borti4938/SNES_MultiRegion_with_DeJitter_QID/installation/SNS-CPU-GPM-02/backside_labeled.jpg

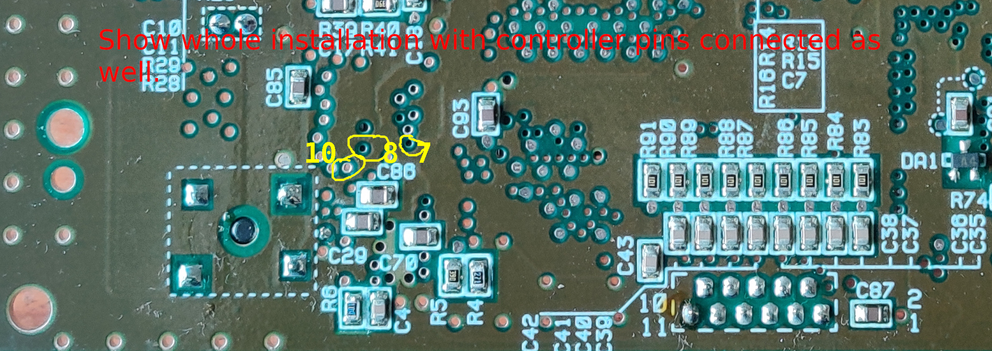
installation/SNS-CPU-GPM-02/backside_labeled.jpg
