borti4938/SNES_MultiRegion_with_DeJitter_QID/installation/SNSP-CPU-01/CIC_Clk.jpg

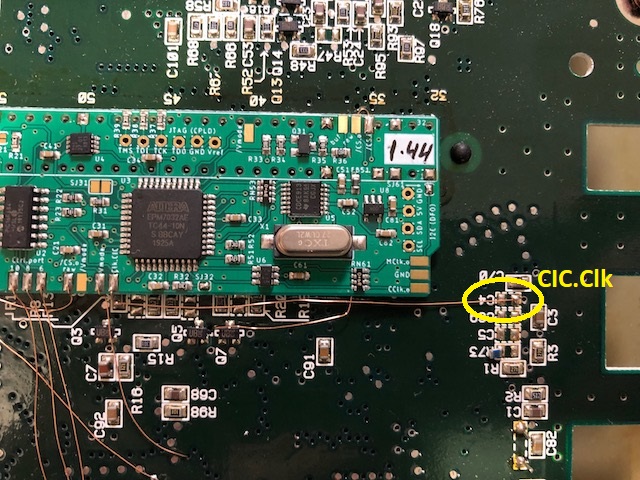
installation/SNSP-CPU-01/CIC_Clk.jpg
