borti4938/SNES_MultiRegion_with_DeJitter_QID/fw/uIGR/snes_uigr_684.asm

    #include <p16f684.inc>

; -----------------------------------------------------------------------
;   SNES "In-game reset" (IGR) controller for use with the SuperCIC only
;
;   Copyright (C) 2010 by Maximilian Rehkopf <otakon@gmx.net>
;
;   Last Modified: Dec. 2015 by Peter Bartmann <borti4938@gmx.de>
;
;   This program is free software; you can redistribute it and/or modify
;   it under the terms of the GNU General Public License as published by
;   the Free Software Foundation; version 2 of the License only.
;
;   This program is distributed in the hope that it will be useful,
;   but WITHOUT ANY WARRANTY; without even the implied warranty of
;   MERCHANTABILITY or FITNESS FOR A PARTICULAR PURPOSE.  See the
;   GNU General Public License for more details.
;
;   You should have received a copy of the GNU General Public License
;   along with this program; if not, write to the Free Software
;   Foundation, Inc., 59 Temple Place, Suite 330, Boston, MA  02111-1307  USA
;
; -----------------------------------------------------------------------
;
;   This program is designed to run on a PIC 16F684 microcontroller connected
;   to the controller port and SNES main board. It allows an SNES to be reset
;   and region switched via a standard controller. This version of the code
;   shall be used only in combination with the SCIC!
;
;   pin configuration: (controller port pin) [other connection]
;
;                                                 ,-----_-----.
;        +5V (1) [mb front 1 and many others :-)] |1        14| GND (7) [mb front 11 and many others :-)]
;   Reset in/out [to CIC pin 8 / SuperCIC pin 13] |2  A5 A0 13| serial data in(4) [mb front 6(*)]
;                           50/60Hz out [to PPUs] |3  A4 A1 12| latch in(3)       [mb front 10]
;               Cart-Region [from SuperCIC pin 3] |4  A3 A2 11| clk in(2)         [mb front 8(**)]
;                        LED out - grn, 50Hz Mode |5  C5 C0 10| LED in - grn [from SuperCIC pin 5]
;                        LED out - red, 60Hz Mode |6  C4 C1  9| LED in - red [from SuperCIC pin 6]
;                 $213f-D4-Patch enable out (***) |7  C3 C2  8| LED_TYPE in  [from SuperCIC pin 7] (****)
;                                                 `-----------'
;
;   (*)
;     use pin 4 at mb front ctrl.panel connector instead of pin 6 if you want to
;     use the IGR-functions with player 2
;   (**)
;     use pin 9 at mb front ctrl.panel connector instead of pin 8 if you want to
;     use the IGR-functions with player 2
;   (***)
;     Pin 7 can be left open if no $213f-D4-Patch is build in the console.
;     Otherwise this pin has to be connected to one input of the 74*133 IC of the
;     patch. Logic is positive.
;   (***)
;     Pin 8 (LED_TYPE) sets the output mode for the LED pins
;     (must be tied to either level):
;       low  = common cathode
;       high = common anode   (output inverted)
;
;
;   As the internal oscillator is used, you should connect a capacitor of about 100nF between
;   Pin 1 (Vdd/+5V) and Pin 14 (Vss/GND) as close as possible to the PIC. This esures best
;   operation
;
;   controller pin numbering
;   ========================
;        _______________________________
;       |                 |             \
;       | (1) (2) (3) (4) | (5) (6) (7)  ) (player 1 or player 2 can be used)
;       |_________________|_____________/
;
;
;   key mapping: L + R + Select +                                (stream data)
;   =============================
;   Start        Reset (normal)                                  0xcf 0xcf
;   X            Reset (double)                                  0xdf 0x8f
;
;   Y            Region 50Hz/PAL                                 0x9f 0xcf
;   A            Region 60Hz/NTSC                                0xdf 0x4f
;   B            Region from Cartridge                           0x5f 0xcf
;   D-Pad left   Region from SCIC                                0xdd 0xcf
;   D-Pad right  Region from SCIC                                0xde 0xcf
;
;   D-Pad up     Toggle the region timeout                       0xd7 0xcf
;   D-Pad down   Toggle $213f-D4-Patch enable/disable            0xdb 0xcf
;
;   Toggle region timeout:
;   LED confirms with
;     - region timeout switched on : red   -> yellow -> green
;     - region timeout switched off: green -> yellow -> red
;
;   Toggle region patch:
;   LED confirms with
;     - region patch switched on : green -> off -> green
;     - region patch switched off: red   -> off -> red
;
;   Lock Type 1:
;   To lock all other combinations one may press (D-Pad left + D-Pad up + L +
;   R + A + X -> strean data 0xf5 0x0f) together. The same combination unlocks
;   the IGR functionalities again.
;   Lock   -> LED confirms with fast flashing red
;   Unlock -> LED confirms with fast flashing green
;
;   Lock Type 2:
;   To lock all combinations one may press (D-Pad down + D-Pad left + L +
;   R + A + B -> strean data 0x79 0x4f) together. This can only be undone by
;   a reset (only reset button, not by sd2snes-IGRs) or power off and on again
;   Lock   -> LED confirms with fast flashing red
;
;
;   functional description:
;   =======================
;   Reset (normal):        simply resets the console.
;   Reset (double):        resets the console twice to enter main menu on
;                          PowerPak (due to initilize a long reset at SCIC)
;                          and sd2snes (double reset detection in firmware).
;
;   Region 50Hz/PAL        overrides the region to 50Hz/PAL.
;   Region 60Hz/NTSC       overrides the region to 60Hz/NTSC.
;   Region from cartridge  sets the region according to the input level of
;                          pin 4 (+5V = 50Hz, 0V = 60Hz).
;   Region from SuperCIC   sets the region according to the input level of
;                          the led (pin 8, 9 and 10) the current mode (50Hz,
;                          60Hz or Auto) is calculated by the uIGR. In this mode
;                          the region is updated periodically.
;
;   Toggle region timeout  for ~9s the console stays in the region mode of the
;                          cartridge and switches then into the last user mode
;   Toggle region patch    enables or disables the d4-patch over pin 7
;                          (0V = disable, +5V = enable)
;
;
;   Support of retro-bit wireless controllers:
;   ==========================================
;   These controllers have a long delay from signalling a button bit change by
;   the SNES until the bit is set on the dataline. This is not a problem if the
;   auto joypad read (AJR) is enabled. However, if AJR is not, this may harm the
;   respondence of the uIGR (as the uIGR might not have enough time to store the
;   button bit). Hence I decided to introduce a new finger breaking button combo
;   to switch on and off the long delays (and hence the support of retro-bit
;   wireless controllers).
;   This combo is:
;     - L+R+St+B+Y+A+X (stream data: 0x2f 0x0f)
;   The uIGR confirms with LED color codes:
;     - support switched on : green -> yellow -> green
;     - support switched off: red   -> yellow -> red
;
;
; -----------------------------------------------------------------------
; Configuration bits: adapt to your setup and needs
    __CONFIG _INTOSCIO & _IESO_OFF & _WDT_OFF & _PWRTE_OFF & _MCLRE_OFF & _CP_OFF & _CPD_OFF & _BOD_OFF

with_lock             set 1 ; 0 = without locking combination
                            ; 1 = with locking combinations
default_with_regpatch set 1 ; 0 = default set to 60Hz and region timeout enabled
                            ; 1 = default set to 60Hz and region patch enabled
                            ;     (for installations without or with region patch)

; -----------------------------------------------------------------------
; macros and definitions

M_movff macro   fromReg, toReg  ; move filereg to filereg
        movfw   fromReg
        movwf   toReg
        endm

M_movpf macro   fromPORT, toReg ; move PORTx to filereg
        movfw   fromPORT
        andlw   0x3f
        movwf   toReg
        endm

M_movlf macro   literal, toReg  ; move literal to filereg
        movlw   literal
        movwf   toReg
        endm

M_beff  macro   compReg1, compReg2, branch  ; branch if two fileregs are equal
        movfw   compReg1
        xorwf   compReg2, w
        btfsc   STATUS, Z
        goto    branch
        endm

M_bepf  macro   compPORT, compReg, branch   ; branch if PORTx equals compReg (ignoring bit 6 and 7)
        movfw   compPORT
        xorwf   compReg, w
        andlw   0x3f
        btfsc   STATUS, Z
        goto    branch
        endm

M_belf  macro   literal, compReg, branch  ; branch if a literal is stored in filereg
        movlw   literal
        xorwf   compReg, w
        btfsc   STATUS, Z
        goto    branch
        endm

M_delay_x05ms   macro   literal ; delay about literal x 05ms
                movlw   literal
                movwf   reg_repetition_cnt
                call    delay_x05ms
                endm

M_T1reset   macro   ; reset and start timer1
            clrf    TMR1L
            clrf    TMR1H
            clrf    PIR1
            bsf     T1CON, TMR1ON
            endm

M_StBuToRegF    macro   button, toReg  ; store button to register (fast)
                btfsc   PORTA, CTRL_DATA
                bsf     toReg, button
                btfss   INTCON, INTF
                goto    $-1
                endm

M_StBuToReg macro   button, toReg  ; store button to register
            btfss   PORTA, CTRL_CLK
            goto    $-1
            nop
            bcf     INTCON, INTF
            btfsc   PORTA, CTRL_DATA
            bsf     toReg, button
            btfss   INTCON, INTF
            goto    $-1
            endm

M_StBuToRegRBWC macro   button, toReg  ; store button to register (Retro-Bit Wireless Controller)
                btfss   PORTA, CTRL_CLK
                goto    $-1
                goto    $+1 ; 2-cycle-delay
                nop
                bcf     INTCON, INTF
                nop
                btfsc   PORTA, CTRL_DATA
                bsf     toReg, button
                btfss   INTCON, INTF
                goto    $-1
                endm

M_push_reset    macro   ; push reset button
                banksel TRISA
                bcf     TRISA, RESET_OUT
                banksel PORTA
                bsf     PORTA, RESET_OUT
                endm

M_release_reset macro   ; push release button
                bcf     PORTA, RESET_OUT
                banksel TRISA
                bsf     TRISA, RESET_OUT
                banksel PORTA
                endm

M_setAuto   macro   ; set modeout to auto
            btfsc   PORTA, CART_MODE_IN
            set50Hz
            btfss   PORTA, CART_MODE_IN
            set60Hz
            endm

#define set60Hz     bcf PORTA, MODE_OUT
#define set50Hz     bsf PORTA, MODE_OUT
#define setD4on     bsf PORTC, REGPATCH_OUT
#define setD4off    bcf PORTC, REGPATCH_OUT

; -----------------------------------------------------------------------
; bits and registers and more

CTRL_DATA       EQU 0
CTRL_LATCH      EQU 1
CTRL_CLK        EQU 2
CART_MODE_IN    EQU 3
MODE_OUT        EQU 4
RESET_IN        EQU 5
RESET_OUT       EQU 5

LED_MODE_50_IN  EQU 0
LED_MODE_60_IN  EQU 1
LED_TYPE_IN     EQU 2
REGPATCH_OUT    EQU 3

reg_ctrl_data_lsb       EQU 0x20
reg_ctrl_data_msb       EQU 0x21
reg_ctrl_read_ready     EQU 0x22
reg_t0_overflows        EQU 0x31
reg_repetition_cnt      EQU 0x32
reg_t1_overflows        EQU 0x33
reg_current_mode        EQU 0x40
reg_passthru_calc       EQU 0x41
reg_led_save            EQU 0x42

bit_mode_scic       EQU 0
bit_mode_auto       EQU 1
bit_mode_50_60      EQU 2
bit_rbwc_support    EQU 3
bit_regtimeout      EQU 4
bit_regpatch        EQU 5

    
code_mode_scic    EQU (1<<bit_mode_scic)      ; 0x01
code_mode_auto    EQU (1<<bit_mode_auto)      ; 0x02
code_mode_60      EQU (0<<bit_mode_50_60)     ; 0x00
code_mode_50      EQU (1<<bit_mode_50_60)     ; 0x04
code_rbwc_support EQU (1<<bit_rbwc_support)   ; 0x08
code_regtimeout   EQU (1<<bit_regtimeout)     ; 0x10
code_regpatch     EQU (1<<bit_regpatch)       ; 0x20

  if with_lock
    bit_igrlock_tmp     EQU 6
    bit_igrlock_ever    EQU 7

    code_igrlock_tmp    EQU (1<<bit_igrlock_tmp)    ; 0x40
  endif

code_led_off    EQU 0x00    ; off
code_led_60     EQU 0x10    ; red
code_led_50     EQU 0x20    ; green
code_led_auto   EQU 0x30    ; yellow
code_invert_led EQU 0x30    ; to invert the LED (needed if a com. anode LED is used)

  if default_with_regpatch
    code_mode_default   EQU (code_mode_60 ^ code_regpatch)
  else
    code_mode_default   EQU (code_mode_60 ^ code_regtimeout)
  endif

delay_05ms_t0_overflows     EQU 0x14    ; prescaler T0 set to 1:2
repetitions_60ms            EQU 0x0c
repetitions_200ms           EQU 0x28
repetitions_260ms           EQU 0x34
repetitions_580ms           EQU 0x74
repetitions_LED_delay       EQU 0x78    ; around 600ms
repetitions_LED_delay_fast  EQU 0x3c    ; around 300ms

overflows_t1_regtimeout_start       EQU 0xa3
overflows_t1_regtimeout_reset       EQU 0xa3
overflows_t1_regtimeout_reset_2     EQU 0x9b
overflows_t1_regtimeout_dblrst      EQU 0xff
overflows_t1_regtimeout_dblrst_2    EQU 0xfb

; -----------------------------------------------------------------------
; buttons

BUTTON_B    EQU 7
BUTTON_Y    EQU 6
BUTTON_SL   EQU 5
BUTTON_ST   EQU 4
DPAD_UP     EQU 3
DPAD_DW     EQU 2
DPAD_LE     EQU 1
DPAD_RI     EQU 0

BUTTON_A    EQU 7
BUTTON_X    EQU 6
BUTTON_L    EQU 5
BUTTON_R    EQU 4

BUTTON_NONE3    EQU 3
BUTTON_NONE2    EQU 2
BUTTON_NONE1    EQU 1
BUTTON_NONE0    EQU 0

; -----------------------------------------------------------------------

; code memory
 org    0x0000
    clrf    STATUS      ; 00h Page 0, Bank 0
    nop                 ; 01h
    nop                 ; 02h
    goto    start       ; 03h Initialisierung / ProgrammBeginn


; --------ISR--------
 org    0x0004  ; jump here on interrupt with GIE set
CtrlRead_ISR
    M_movlf ((1<<INTE)^(1<<RAIE)), INTCON
    btfsc   reg_current_mode, bit_rbwc_support
    goto    CtrlRead_ISR_RBWC
    
; button B can be read immediately (nearly, 4 instruction cycles until this  macro is reached)
    M_StBuToRegF  BUTTON_B, reg_ctrl_data_msb
    
; before button Y is stored, unset RAIF (from now on, no IOC at the data latch shall appear)
    btfss   PORTA, CTRL_CLK
    goto    $-1
    bcf     INTCON, INTF
    bcf     INTCON, RAIF
    M_StBuToRegF  BUTTON_Y, reg_ctrl_data_msb

; read all other buttons afterwards
    M_StBuToReg BUTTON_SL, reg_ctrl_data_msb
    M_StBuToReg BUTTON_ST, reg_ctrl_data_msb
    M_StBuToReg DPAD_UP,   reg_ctrl_data_msb
    M_StBuToReg DPAD_DW,   reg_ctrl_data_msb
    M_StBuToReg DPAD_LE,   reg_ctrl_data_msb
    M_StBuToReg DPAD_RI,   reg_ctrl_data_msb
    
    M_StBuToReg BUTTON_A,     reg_ctrl_data_lsb
    M_StBuToReg BUTTON_X,     reg_ctrl_data_lsb
    M_StBuToReg BUTTON_L,     reg_ctrl_data_lsb
    M_StBuToReg BUTTON_R,     reg_ctrl_data_lsb
    M_StBuToReg BUTTON_NONE3, reg_ctrl_data_lsb
    M_StBuToReg BUTTON_NONE2, reg_ctrl_data_lsb
    M_StBuToReg BUTTON_NONE1, reg_ctrl_data_lsb
    M_StBuToReg BUTTON_NONE0, reg_ctrl_data_lsb

    goto  check_controller_read
    
CtrlRead_ISR_RBWC
; button B can be read immediately (nearly, 5 instruction cycles until this  macro is reached)
    M_StBuToRegF  BUTTON_B, reg_ctrl_data_msb
    
; before button Y is stored, unset RAIF (from now on, no IOC at the data latch shall appear)
    btfss   PORTA, CTRL_CLK
    goto    $-1
    goto    $+1  ; 2-cycle-delay
    nop
    bcf     INTCON, INTF
    bcf     INTCON, RAIF
    M_StBuToRegF  BUTTON_Y, reg_ctrl_data_msb

; read all other buttons afterwards
    M_StBuToRegRBWC BUTTON_SL, reg_ctrl_data_msb
    M_StBuToRegRBWC BUTTON_ST, reg_ctrl_data_msb
    M_StBuToRegRBWC DPAD_UP,   reg_ctrl_data_msb
    M_StBuToRegRBWC DPAD_DW,   reg_ctrl_data_msb
    M_StBuToRegRBWC DPAD_LE,   reg_ctrl_data_msb
    M_StBuToRegRBWC DPAD_RI,   reg_ctrl_data_msb
    
    M_StBuToRegRBWC BUTTON_A,     reg_ctrl_data_lsb
    M_StBuToRegRBWC BUTTON_X,     reg_ctrl_data_lsb
    M_StBuToRegRBWC BUTTON_L,     reg_ctrl_data_lsb
    M_StBuToRegRBWC BUTTON_R,     reg_ctrl_data_lsb
    M_StBuToRegRBWC BUTTON_NONE3, reg_ctrl_data_lsb
    M_StBuToRegRBWC BUTTON_NONE2, reg_ctrl_data_lsb
    M_StBuToRegRBWC BUTTON_NONE1, reg_ctrl_data_lsb
    M_StBuToRegRBWC BUTTON_NONE0, reg_ctrl_data_lsb

check_controller_read
    btfsc   INTCON, RAIF            ; another IOC on data latch appeared
    goto    invalid_controller_read ; -> if yes, invalid read
    bsf	    reg_ctrl_read_ready, 0  ; -> if no, indicate a valid read is stored
    return                          ; return with GIE still unset (GIE is set again on demand)

invalid_controller_read
    clrf    INTCON
    clrf    reg_ctrl_data_msb
    clrf    reg_ctrl_data_lsb
    clrf    reg_ctrl_read_ready
    bsf	    INTCON, RAIE
    retfie                      ; return with GIE set


; --------IDLE loops--------
check_scic_auto
    clrf    INTCON
    btfsc   PORTA, RESET_IN                 ; reset button pressed?
    goto    check_reset                     ; then the SCIC might get a new mode or the console is reset
    btfsc   reg_current_mode, bit_mode_scic ; SCIC-Mode?
    goto    setregion_passthru              ; if yes, check the current state
    btfsc   reg_current_mode, bit_mode_auto ; Auto-Mode?
    goto    setregion_auto_woLED            ; if yes, check the current state

idle_prepare
    if with_lock
      btfsc   reg_current_mode, bit_igrlock_ever
      goto    check_scic_auto
    endif

    clrf    reg_ctrl_data_msb
    clrf    reg_ctrl_data_lsb
    clrf    reg_ctrl_read_ready
    M_T1reset

    btfsc   PORTA, CTRL_LATCH   ; data latch currently high?
    call    CtrlRead_ISR        ; if yes -> go go go
    M_movlf ((1<<GIE)^(1<<RAIE)), INTCON    ; set GIE, only react on RAIF

idle_loop
    btfsc   reg_ctrl_read_ready, 0
    goto    checkkeys
    btfsc   PORTA, RESET_IN   ; reset button pressed?
    goto    check_reset       ; then the SCIC might get a new mode or the console is reset
    btfss   PIR1, TMR1IF      ; timer 1 overflow?
    goto    check_scic_auto   ; SNES hasn't read controller past ~65ms
    goto    idle_loop


; --------controller routines--------
checkkeys
    clrf    INTCON
  if with_lock
    M_belf  0xf5, reg_ctrl_data_msb, un_lock_igr_tmp  ; check for (un)lock igr before doin' anything else
    btfsc   reg_current_mode, bit_igrlock_tmp         ; igr locked?
    goto    check_scic_auto                           ; yes
  endif
    M_belf  0x4f, reg_ctrl_data_lsb, group4f
    M_belf  0x8f, reg_ctrl_data_lsb, group8f
    M_belf  0xcf, reg_ctrl_data_lsb, groupcf
    M_belf  0x0f, reg_ctrl_data_lsb, rbwc_support
    goto    check_scic_auto

group4f ; check L+R+sel+...
    M_belf  0xdf, reg_ctrl_data_msb, doregion_60    ; A
  if with_lock
    M_belf  0x79, reg_ctrl_data_msb, lock_igr_ever  ; Dw+Le+A+B
  endif
    goto    check_scic_auto

group8f ; check L+R+sel+X
    M_movlf overflows_t1_regtimeout_dblrst, reg_t1_overflows  ; in case of reg.timout is enabled
    M_belf  0xdf, reg_ctrl_data_msb, doreset_dbl              ; do dbl reset
    goto    check_scic_auto

groupcf ; check L+R+sel+...
    M_movlf overflows_t1_regtimeout_reset, reg_t1_overflows ; in case of reg.timout is enabled
    M_belf  0xcf, reg_ctrl_data_msb, doreset_normal         ; start
    M_belf  0x5f, reg_ctrl_data_msb, doregion_auto          ; B
    M_belf  0x9f, reg_ctrl_data_msb, doregion_50            ; Y
    M_belf  0xd7, reg_ctrl_data_msb, toggle_startup         ; Up
    M_belf  0xdb, reg_ctrl_data_msb, toggle_d4_patch        ; Down
    M_belf  0xdd, reg_ctrl_data_msb, doscic_passthru        ; Left
    M_belf  0xde, reg_ctrl_data_msb, doscic_passthru        ; Right
    goto    check_scic_auto


doreset_dbl
    M_push_reset
    call    delay_05ms
    call    delay_05ms
    call    delay_05ms
    call    delay_05ms
    M_release_reset
    M_delay_x05ms   repetitions_200ms

doreset_normal
    M_push_reset
    call    delay_05ms
    call    delay_05ms
    btfsc   reg_current_mode, bit_regtimeout  ; region timeout enabled?
    call    call_M_setAuto                    ; if yes, define the output to the S-CPUN/PPUs
    call    delay_05ms
    call    delay_05ms
    M_release_reset
    btfss   reg_current_mode, bit_regtimeout  ; region timout disabled?
    goto    doreset_end                       ; if yes, go on with 'normal procedure'

    M_T1reset                                 ; start timer 1
    goto    regtimeout                        ; if no, we had to perform a region timeout

doreset_end ; short delay - time for the user to release the button combination
    M_movlf repetitions_580ms, reg_repetition_cnt
    btfsc   reg_current_mode, bit_mode_scic ; SCIC-Mode?
    goto    doreset_end_scic_mode           ; if yes, split up delays
    call    delay_x05ms 
    goto    check_scic_auto

doreset_end_scic_mode ; delay is split up as the LED state is not updated during
                      ; the delay call
    call    setled_passthru
    call    delay_05ms
    decfsz  reg_repetition_cnt, 1
    goto    doreset_end_scic_mode
    goto    setregion_passthru

doregion_auto
    movfw   reg_current_mode
    andlw   0x78              ; save the igr_lock, reg_timeout, reg_patch and rbwc_support
    xorlw   code_mode_auto    ; set mode auto
    movwf   reg_current_mode
    call    save_mode

setregion_auto
    call    setled_auto

setregion_auto_woLED
    M_setAuto
    goto    idle_prepare

doregion_60
    movfw   reg_current_mode
    andlw   0x78              ; save the igr_lock, reg_timeout, reg_patch and rbwc_support
;    xorlw   code_mode_60      ; set mode 60
    movwf   reg_current_mode
    call    save_mode

setregion_60
    call    setled_60

setregion_60_woLED
    set60Hz
    goto    idle_prepare

doregion_50
    movfw   reg_current_mode
    andlw   0x78              ; save the igr_lock, reg_timeout, reg_patch and rbwc_support
    xorlw   code_mode_50      ; set mode 50
    movwf   reg_current_mode
    call    save_mode

setregion_50
    call    setled_50

setregion_50_woLED
    set50Hz
    goto    idle_prepare


toggle_startup
    movfw   reg_current_mode
    xorlw   code_regtimeout                   ; toggle
    movwf   reg_current_mode
    call    save_mode
    btfsc   reg_current_mode, bit_regtimeout  ; reg_timeout now disabled?
    goto    LED_confirm_rt_1                  ; if enabled, confirm with r-y-gr

LED_confirm_rt_0 ; LED fading pattern: off->green->yellow->red->off->last LED color
    M_movpf         PORTC, reg_led_save ; save last LED color and d4
    call            setled_off
    M_delay_x05ms   repetitions_LED_delay
    call            setled_50
    M_delay_x05ms   repetitions_LED_delay
    call            setled_auto
    M_delay_x05ms   repetitions_LED_delay
    call            setled_60
    M_delay_x05ms   repetitions_LED_delay
    call            setled_off
    M_delay_x05ms   repetitions_LED_delay
    M_movff         reg_led_save, PORTC ; return to last LED color
    goto            check_scic_auto

LED_confirm_rt_1 ; LED fading pattern: off->red->yellow->green->off->last LED color
    M_movpf         PORTC, reg_led_save ; save last LED color and d4
    call            setled_off
    M_delay_x05ms   repetitions_LED_delay
    call            setled_60
    M_delay_x05ms   repetitions_LED_delay
    call            setled_auto
    M_delay_x05ms   repetitions_LED_delay
    call            setled_50
    M_delay_x05ms   repetitions_LED_delay
    call            setled_off
    M_delay_x05ms   repetitions_LED_delay
    M_movff         reg_led_save, PORTC ; return to last LED color
    goto            check_scic_auto

toggle_d4_patch
    movfw   reg_current_mode
    xorlw   code_regpatch                   ; toggle
    movwf   reg_current_mode
    call    save_mode
    btfsc   reg_current_mode, bit_regpatch  ; region patch now disabled?
    goto    enable_d4_patch                 ; if no, enable it

disable_d4_patch ; otherwise disable d4-patch
    setD4off

LED_confirm_d4off   ; LED fading pattern: off->red->off->red->off->last LED color
    M_movpf         PORTC, reg_led_save ; save last LED color and d4
    call            setled_off
    M_delay_x05ms   repetitions_LED_delay
    call            setled_60
    M_delay_x05ms   repetitions_LED_delay
    call            setled_off
    M_delay_x05ms   repetitions_LED_delay
    call            setled_60
    M_delay_x05ms   repetitions_LED_delay
    call            setled_off
    M_delay_x05ms   repetitions_LED_delay
    M_movff         reg_led_save, PORTC ; return to last LED color
    goto            check_scic_auto

enable_d4_patch ; enable d4-patch
    setD4on

LED_confirm_d4on    ; LED fading pattern: off->green->off->green->off->last LED color
    M_movpf         PORTC, reg_led_save ; save last LED color and d4
    call            setled_off
    M_delay_x05ms   repetitions_LED_delay
    call            setled_50
    M_delay_x05ms   repetitions_LED_delay
    call            setled_off
    M_delay_x05ms   repetitions_LED_delay
    call            setled_50
    M_delay_x05ms   repetitions_LED_delay
    call            setled_off
    M_delay_x05ms   repetitions_LED_delay
    M_movff         reg_led_save, PORTC ; return to last LED color
    goto            check_scic_auto

  if with_lock
    un_lock_igr_tmp ; check for (un)lock the irg
        M_belf  0x0f, reg_ctrl_data_lsb, toggle_igrlock_tmp ; check the LSBs
        goto    check_scic_auto                             ; if stream data is not matched, go back to check_scic_auto

    toggle_igrlock_tmp
        movfw   reg_current_mode
        xorlw   code_igrlock_tmp                    ; toggle
        movwf   reg_current_mode
        call    save_mode
        btfsc   reg_current_mode, bit_igrlock_tmp   ; irg now unlocked?
        goto    LED_confirm_lock_igr                ; if no, conform locking

    LED_confirm_unlock_igr ; LED fast flashing green
        M_movpf         PORTC, reg_led_save ; save last LED color and d4
        call            setled_off
        M_delay_x05ms   repetitions_LED_delay_fast
        call            setled_50
        M_delay_x05ms   repetitions_LED_delay_fast
        call            setled_off
        M_delay_x05ms   repetitions_LED_delay_fast
        call            setled_50
        M_delay_x05ms   repetitions_LED_delay_fast
        call            setled_off
        M_delay_x05ms   repetitions_LED_delay_fast
        call            setled_50
        M_delay_x05ms   repetitions_LED_delay_fast
        call            setled_off
        M_delay_x05ms   repetitions_LED_delay_fast
        call            setled_50
        M_delay_x05ms   repetitions_LED_delay_fast
        call            setled_off
        M_delay_x05ms   repetitions_LED_delay_fast
        call            setled_50
        M_delay_x05ms   repetitions_LED_delay_fast
        call            setled_off
        M_delay_x05ms   repetitions_LED_delay_fast
        M_movff         reg_led_save, PORTC ; return to last LED color
        goto            check_scic_auto

    lock_igr_ever
        bsf     reg_current_mode, bit_igrlock_ever

    LED_confirm_lock_igr ; LED fast flashing red
        M_movpf         PORTC, reg_led_save ; save last LED color and d4
        call            setled_off
        M_delay_x05ms   repetitions_LED_delay_fast
        call            setled_60
        M_delay_x05ms   repetitions_LED_delay_fast
        call            setled_off
        M_delay_x05ms   repetitions_LED_delay_fast
        call            setled_60
        M_delay_x05ms   repetitions_LED_delay_fast
        call            setled_off
        M_delay_x05ms   repetitions_LED_delay_fast
        call            setled_60
        M_delay_x05ms   repetitions_LED_delay_fast
        call            setled_off
        M_delay_x05ms   repetitions_LED_delay_fast
        call            setled_60
        M_delay_x05ms   repetitions_LED_delay_fast
        call            setled_off
        M_delay_x05ms   repetitions_LED_delay_fast
        call            setled_60
        M_delay_x05ms   repetitions_LED_delay_fast
        call            setled_off
        M_delay_x05ms   repetitions_LED_delay_fast
        M_movff         reg_led_save, PORTC ; return to last LED color
        goto            check_scic_auto
  endif

rbwc_support
    M_belf  0x2f, reg_ctrl_data_msb, toggle_rbwc_support  ; check the MSBs
    goto    check_scic_auto                               ; if stream data is not matched, go back to check_scic_auto

toggle_rbwc_support
    movfw   reg_current_mode
    xorlw   code_rbwc_support                   ; toggle
    movwf   reg_current_mode
    call    save_mode
    btfss   reg_current_mode, bit_rbwc_support  ; support switched on?
    goto    LED_confirm_rbwc_support_off        ; if no, conform switching off

LED_confirm_rbwc_support_on   ; LED fading pattern: off->green->yellow->green->off->last LED color
    M_movpf         PORTC, reg_led_save ; save last LED color and d4
    call            setled_off
    M_delay_x05ms   repetitions_LED_delay
    call            setled_50
    M_delay_x05ms   repetitions_LED_delay
    call            setled_auto
    M_delay_x05ms   repetitions_LED_delay
    call            setled_50
    M_delay_x05ms   repetitions_LED_delay
    call            setled_off
    M_delay_x05ms   repetitions_LED_delay
    M_movff         reg_led_save, PORTC ; return to last LED color
    goto            check_scic_auto

LED_confirm_rbwc_support_off   ; LED fading pattern: off->red->yellow->red->off->last LED color
    M_movpf         PORTC, reg_led_save ; save last LED color and d4
    call            setled_off
    M_delay_x05ms   repetitions_LED_delay
    call            setled_60
    M_delay_x05ms   repetitions_LED_delay
    call            setled_auto
    M_delay_x05ms   repetitions_LED_delay
    call            setled_60
    M_delay_x05ms   repetitions_LED_delay
    call            setled_off
    M_delay_x05ms   repetitions_LED_delay
    M_movff         reg_led_save, PORTC ; return to last LED color
    goto            check_scic_auto

; --------reset-button routines--------
check_reset
    clrf    INTCON
    call    delay_05ms      ; software debounce
    call    delay_05ms      ; -- needed in case of region timeout is enabled
    call    delay_05ms
    btfss   PORTA, RESET_IN ; reset still pressed?
    goto    check_scic_auto

    M_movpf PORTC, reg_passthru_calc

check_reset_loop
    btfsc   PORTA, RESET_IN                 ; reset still pressed?
    goto    wait_for_rstloop_scic_passthru  ; if yes, the user might want to change the mode of the SCIC

check_reset_prepare_timeout
    if with_lock
      bcf     reg_current_mode, bit_igrlock_ever
    endif
    btfss   reg_current_mode, bit_regtimeout  ; region timeout disabled?
    goto    check_scic_auto                   ; if yes, go on with 'normal procedure'
    M_setAuto                                 ; if no, predefine the auto-mode ...

    call    delay_05ms  ; software debounce
    M_setAuto
    call    delay_05ms  ; software debounce
    M_setAuto
    call    delay_05ms  ; software debounce
    M_setAuto

    clrf    TMR0        ; start timer (operation clears prescaler of T0)
    banksel TRISA
    movfw   OPTION_REG
    andlw   0xf0
    movwf   OPTION_REG
    banksel PORTA
    M_movlf repetitions_580ms, reg_repetition_cnt
    M_movlf delay_05ms_t0_overflows, reg_t0_overflows
    M_movlf (1<<T0IE), INTCON ; enable timer 0 interrupt

check_dblrst
    btfsc   PORTA, RESET_IN   ; reset pressed again?
    goto    check_dblrst_prepare_timeout
    M_setAuto
    btfss   INTCON, T0IF
    goto    check_dblrst
    bcf     INTCON, T0IF
    decfsz  reg_t0_overflows, 1
    goto    check_dblrst
    M_movlf delay_05ms_t0_overflows, reg_t0_overflows
    decfsz  reg_repetition_cnt, 1
    goto    check_dblrst

    clrf    INTCON            ; disable timer 0 interrupt
    M_movlf overflows_t1_regtimeout_reset_2, reg_t1_overflows
    M_T1reset                 ; start timer 1
    goto    regtimeout        ; ...and perform a region timeout

check_dblrst_prepare_timeout
    clrf    INTCON            ; disable timer 0 interrupt
    M_movlf overflows_t1_regtimeout_dblrst_2, reg_t1_overflows
    M_T1reset                 ; start timer 1
    goto    regtimeout        ; ...and perform a region timeout

wait_for_rstloop_scic_passthru
    M_bepf  PORTC, reg_passthru_calc, check_reset_loop ; go back to check_reset_loop if LED not changed by S-CIC

rstloop_scic_passthru
    call    setled_passthru
    btfsc   PORTA, RESET_IN       ; reset still pressed?
    goto    rstloop_scic_passthru

doscic_passthru
    movfw   reg_current_mode
    andlw   0x78              ; save the igr_lock, reg_timeout, reg_patch and rbwc_support
    xorlw   code_mode_scic    ; set mode scic
    movwf   reg_current_mode
    call    save_mode

setregion_passthru
    call    setled_passthru

setregion_passthru_woLED
    M_movff PORTC, reg_passthru_calc
    btfss   reg_passthru_calc, LED_TYPE_IN
    goto    setregion_passthru_woLED_Ca

setregion_passthru_woLED_An
    btfsc   reg_passthru_calc, LED_MODE_50_IN
    goto    setregion_60_woLED    ; SCIC: green off -> red must be on
                                  ; SCIC: green on & ...
    btfsc   reg_passthru_calc, LED_MODE_60_IN
    goto    setregion_50_woLED    ; ... red off
    goto    setregion_auto_woLED  ; ... red on

setregion_passthru_woLED_Ca
    btfss   reg_passthru_calc, LED_MODE_50_IN
    goto    setregion_60_woLED    ; SCIC: green off -> red must be on
                                  ; SCIC: green on & ...
    btfss   reg_passthru_calc, LED_MODE_60_IN
    goto    setregion_50_woLED    ; ... red off
    goto    setregion_auto_woLED  ; ... red on


; --------mode, led, delay and save_mode calls--------
call_M_setAuto
    M_setAuto
    return

setled_60
    movfw   PORTC
    andlw   0x0f                ; save d4
    xorlw   code_led_60         ; set LED
    btfsc   PORTC, LED_TYPE_IN  ; if common anode:
    xorlw   code_invert_led     ; invert output
    movwf   PORTC
    return

setled_50
    movfw   PORTC
    andlw   0x0f                ; save d4
    xorlw   code_led_50         ; set LED
    btfsc   PORTC, LED_TYPE_IN  ; if common anode:
    xorlw   code_invert_led     ; invert output
    movwf   PORTC
    return

setled_auto
    movfw   PORTC
    andlw   0x0f                ; save d4
    xorlw   code_led_auto       ; set LED
    btfsc   PORTC, LED_TYPE_IN  ; if common anode:
    xorlw   code_invert_led     ; invert output
    movwf   PORTC
    return

setled_passthru
    movfw   PORTC
    andlw   0x0f                    ; save d4
    btfsc   PORTC, LED_MODE_50_IN   ; green LED
    xorlw   code_led_50
    btfsc   PORTC, LED_MODE_60_IN   ; red LED
    xorlw   code_led_60
    movwf   PORTC
    return

setled_off
    movfw   PORTC
    andlw   0x0f                ; save d4
    xorlw   code_led_off        ; set LED
    btfsc   PORTC, LED_TYPE_IN  ; if common anode:
    xorlw   code_invert_led     ; invert output
    movwf   PORTC
    return

save_mode
    movfw   reg_current_mode
    banksel EEADR
    movwf   EEDAT
    clrf    EEADR             ; address 0
    bsf     EECON1,WREN
    M_movlf 0x55, EECON2
    M_movlf 0xaa, EECON2
    bsf     EECON1, WR
wait_save_mode_end
    btfsc   EECON1, WR
    goto    wait_save_mode_end
    bcf     EECON1, WREN
    banksel PORTA
    return

delay_05ms
    clrf    TMR0                ; start timer (operation clears prescaler of T0)
    banksel TRISA
    movfw   OPTION_REG
    andlw   0xf0
    movwf   OPTION_REG
    banksel PORTA
    M_movlf delay_05ms_t0_overflows, reg_t0_overflows
    M_movlf (1<<T0IE), INTCON   ; enable timer 0 interrupt
delay_05ms_loop_pre
    bcf     INTCON, T0IF
delay_05ms_loop
    btfsc   reg_current_mode, bit_mode_scic ; SCIC-Mode?
    call    delay_update_scic_mode          ; if yes, check the current state
    btfsc   reg_current_mode, bit_mode_auto ; Auto-Mode?
    call    delay_update_auto_mode          ; if yes, check the current state
    btfss   INTCON, T0IF
    goto    delay_05ms_loop
    decfsz  reg_t0_overflows, 1
    goto    delay_05ms_loop_pre
    clrf    INTCON              ; disable timer 0 interrupt
    return

delay_update_auto_mode
    M_setAuto
    return

delay_update_scic_mode
    M_movff PORTC, reg_passthru_calc
    btfss   reg_passthru_calc, LED_TYPE_IN
    goto    delay_update_scic_mode_Ca
delay_update_scic_mode_An
    btfsc   reg_passthru_calc, LED_MODE_50_IN
    goto    delay_update_scic_mode_60Hz       ; SCIC: green off -> red must be on
                                              ; SCIC: green on & ...
    btfsc   reg_passthru_calc, LED_MODE_60_IN
    goto    delay_update_scic_mode_50Hz       ; ... red off
    M_setAuto                                 ; ... red on
    return
delay_update_scic_mode_Ca
    btfss   reg_passthru_calc, LED_MODE_50_IN
    goto    delay_update_scic_mode_60Hz       ; SCIC: green off -> red must be on
                                              ; SCIC: green on & ...
    btfss   reg_passthru_calc, LED_MODE_60_IN
    goto    delay_update_scic_mode_50Hz       ; ... red off
    M_setAuto                                 ; ... red on
    return
delay_update_scic_mode_60Hz
    set60Hz
    return
delay_update_scic_mode_50Hz
    set50Hz
    return

delay_x05ms
    call    delay_05ms
    decfsz  reg_repetition_cnt, 1
    goto    delay_x05ms
    return


; --------initialization--------
start
    clrf    PORTA
    clrf    PORTC
    M_movlf 0x07, CMCON0      ; PORTA2..0 are digital I/O (not connected to comparator)
    clrf    INTCON            ; INTCON set on demand during program
    banksel TRISA
    M_movlf 0x70, OSCCON      ; use 8MHz internal clock (internal clock set on config)
    clrf    ANSEL
    M_movlf 0x2f, TRISA       ; in out in in in in
    M_movlf 0x07, TRISC       ; out out out in in in
    M_movlf 0x00, WPUA        ; no pullups
    M_movlf 0x02, IOCA        ; IOC on CTRL_LATCH
    M_movlf 0x80, OPTION_REG  ; global pullup disable, use falling clock edge for INTE, prescaler assigned to T0 (1:2)
    banksel PORTA
    M_movlf 0x10, T1CON       ; set prescaler T1 1:2

    set60Hz ; assume NTSC-Mode
    setD4on ; assume D4-Patch on

load_mode
    clrf    reg_current_mode
    bcf     STATUS, C   ; clear carry
    banksel EEADR       ; fetch current mode from EEPROM
    clrf    EEADR       ; address 0
    bsf     EECON1, RD
    movfw   EEDAT
    banksel PORTA
  if with_lock
    andlw   0x7f        ; unset potential permanent lock
  else
    andlw   0x3f        ; unset all unused bits
  endif
    movwf   reg_current_mode

check_d4_mode
    btfss   reg_current_mode, bit_regpatch  ; region patching disabled?
    setD4off

check_last_led
    btfsc   reg_current_mode, bit_mode_scic   ; last mode from SCIC?
    goto    check_last_led_scic
    btfsc   reg_current_mode, bit_mode_auto   ; last mode "Auto"?
    goto    check_last_led_auto
    btfss   reg_current_mode, bit_mode_50_60  ; last mode "60Hz"?
    goto    check_last_led_60
;    btfsc   reg_current_mode, bit_mode_50_60   ; last mode "50Hz"?
;    goto    check_last_led_50

check_last_led_50
    call    setled_50
    goto    check_reg_timeout
check_last_led_60
    call    setled_60
    goto    check_reg_timeout
check_last_led_auto
    call    setled_auto
    goto    check_reg_timeout
check_last_led_scic
    call    setled_passthru
;    goto    check_reg_timeout


check_reg_timeout
    btfss   reg_current_mode, bit_regtimeout  ; regtimeout disabled?
    goto    last_mode_check                   ; if yes, jump directly to the last mode chosen
    movlw   overflows_t1_regtimeout_start
    movwf   reg_t1_overflows

    M_T1reset                                  ; start timer 1

regtimeout
    M_setAuto
    btfsc   reg_current_mode, bit_mode_scic
    call    setled_passthru
    btfss   PIR1, TMR1IF                    ; timer 1 overflow?
    goto    regtimeout
    clrf    PIR1                            ; clear overflow bit
    decfsz  reg_t1_overflows                ; Are all loops done?
    goto    regtimeout                      ; If no, repeat this loop

    bcf     T1CON, TMR1ON

last_mode_check
    btfsc   reg_current_mode, bit_mode_scic   ; last mode from SCIC?
    goto    setregion_passthru_woLED
    btfsc   reg_current_mode, bit_mode_auto   ; last mode "Auto"?
    goto    setregion_auto_woLED
    btfss   reg_current_mode, bit_mode_50_60  ; last mode "60Hz"?
    goto    setregion_60_woLED
;    btfsc   reg_current_mode, bit_mode_50_60  ; last mode "50Hz"?
    goto    setregion_50_woLED

; -----------------------------------------------------------------------
; eeprom data
DEEPROM CODE
    de  code_mode_default

theveryend
    end
; ------------------------------------------------------------------------
